mikeysklar/pi-debug-swd-adapter/kicad/pico-debug-swd-adapter.kicad_sch

## KiCad design kicad/pico-debug-swd-adapter.kicad_sch (2026-07-26)

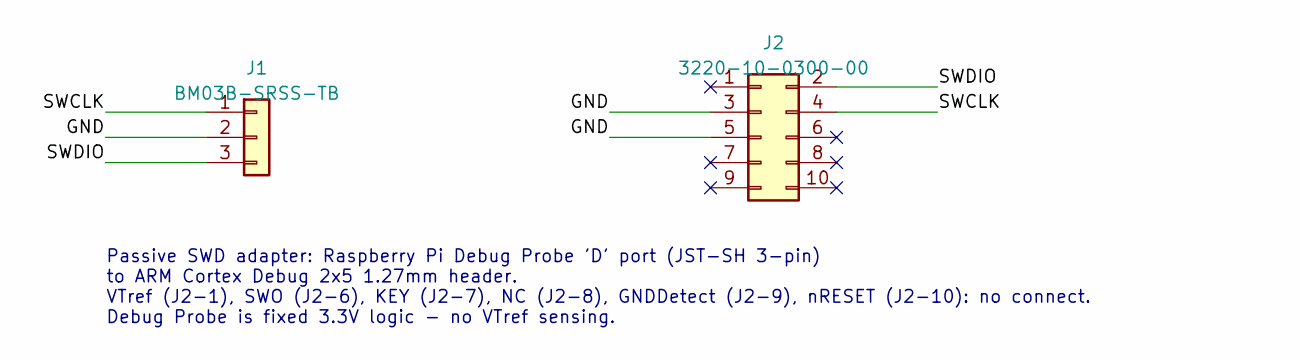
[picture p11: schematic pico-debug-swd-adapter.kicad_sch]

Parts:
J1: BM03B-SRSS-TB; JST_SH_BM03B-SRSS-TB_1x03-1MP_P1.00mm_Vertical
J2: 3220-10-0300-00; PinHeader_2x05_P1.27mm_Vertical_SMD

Connections:
GND: J1.2, J2.3, J2.5
SWCLK: J1.1, J2.4
SWDIO: J1.3, J2.2

Notes on the sheet:
Passive SWD adapter: Raspberry Pi Debug Probe 'D' port (JST-SH 3-pin) to ARM Cortex Debug 2x5 1.27mm header. VTref (J2-1), SWO (J2-6), KEY (J2-7), NC (J2-8), GNDDetect (J2-9), nRESET (J2-10): no connect. Debug Probe is fixed 3.3V logic - no VTref sensing.
